djarty24/hacker-card/img/pcb-art.jpg

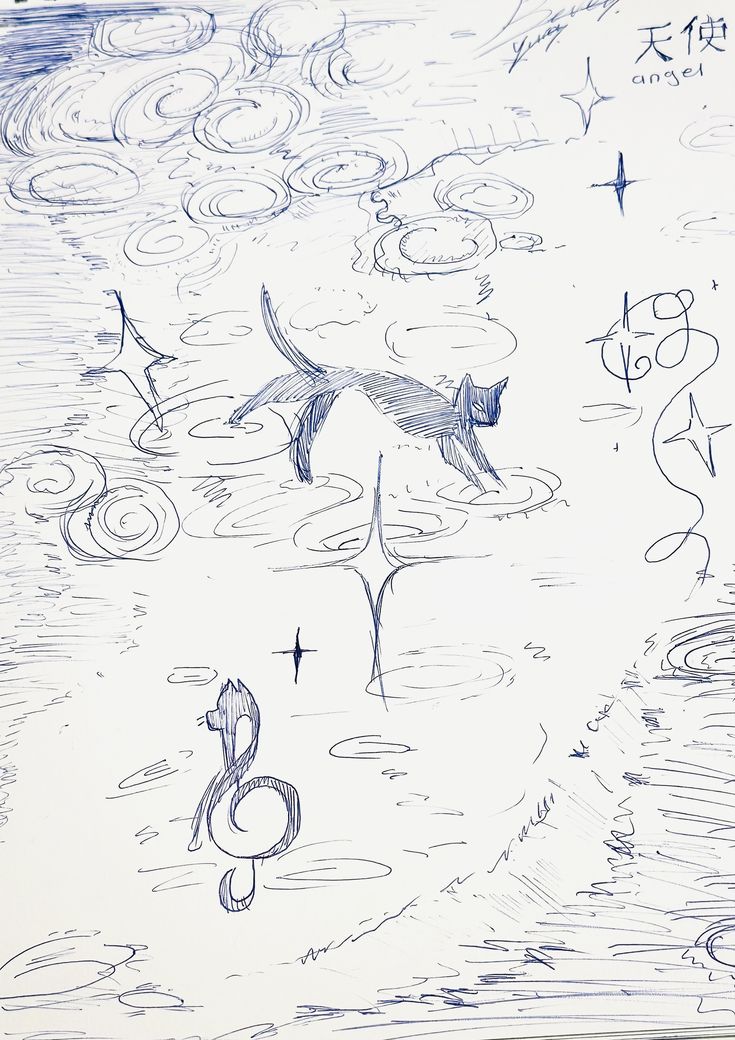
img/pcb-art.jpg
